SJSU-CMPE-195/group-project-group-22/hardware/schematics/Circuit Images/NeuronSynapseVersion1.jpg

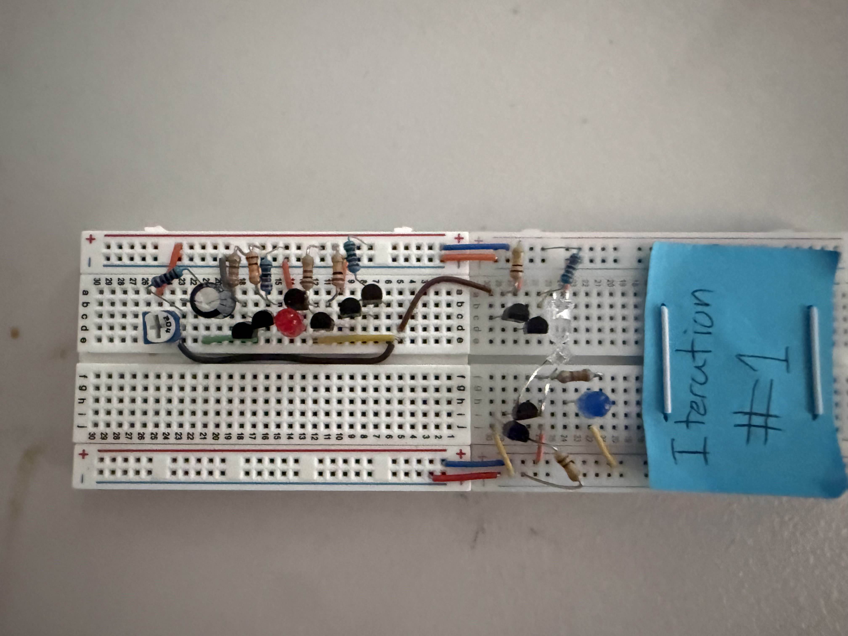
hardware/schematics/Circuit Images/NeuronSynapseVersion1.jpg
