SJSU-CMPE-195/group-project-group-22/hardware/schematics/Circuit Images/NeuronSynapseVersion2.jpg

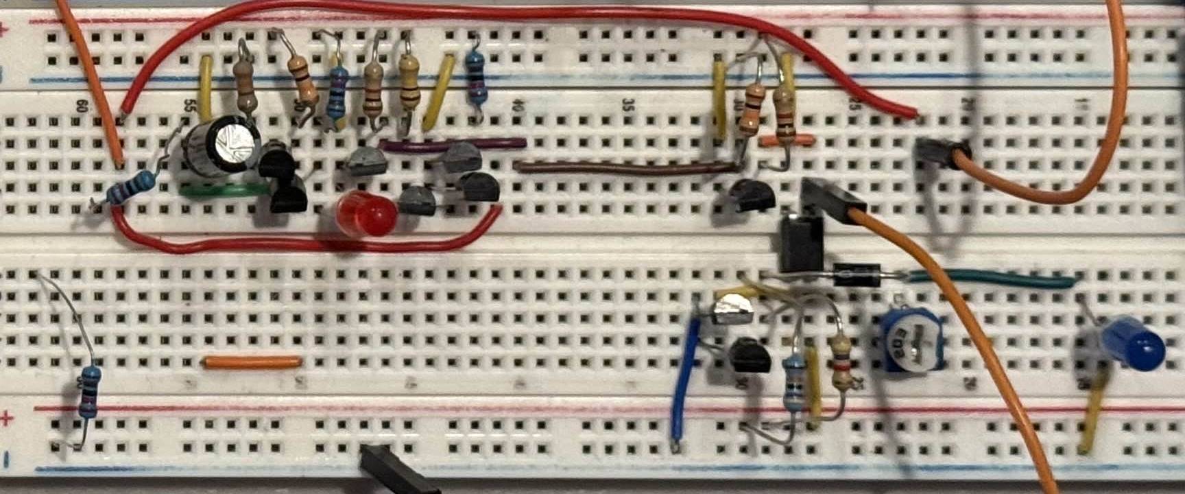
hardware/schematics/Circuit Images/NeuronSynapseVersion2.jpg
