SJSU-CMPE-195/group-project-group-22/hardware/pcb/PCB Soldering Images/PCB2.jpg

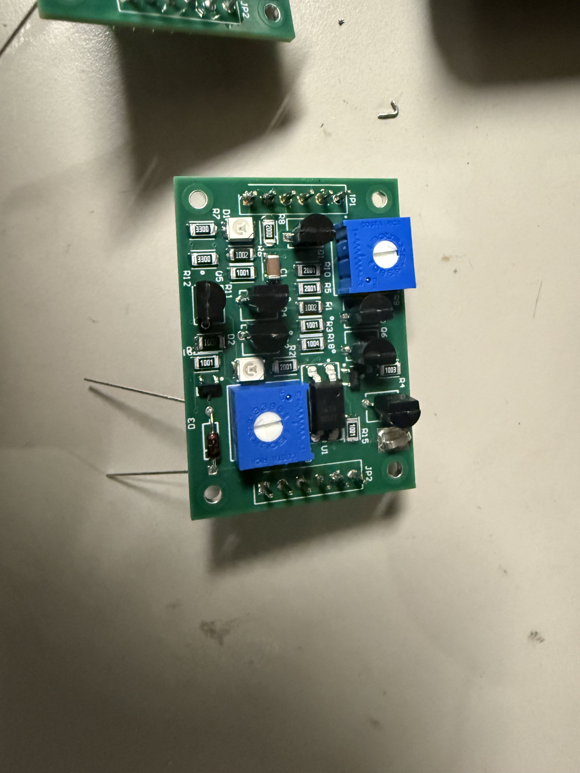
hardware/pcb/PCB Soldering Images/PCB2.jpg
