SJSU-CMPE-195/group-project-group-22/hardware/schematics/Neuron-Synapse-Version7-Schematic.asc

C1: cap; 47µF
C2: cap; 47µF
C3: cap; 47µF
D1: LED
D2: diode
D3: zener
D4: LED
D5: diode
D6: zener
D7: LED
D8: diode
D9: LED
M1: nmos; 2N7002
M2: nmos; 2N7002
M3: nmos; 2N7002
M4: nmos; 2N7002
M5: nmos; 2N7002
M6: nmos; 2N7002
Q1: npn; 2N2222
Q2: npn; 2N2222
Q3: npn; 2N2222
Q4: npn; 2N2222
Q5: npn; 2N2222
Q6: npn; 2N2222
Q7: npn; 2N2222
Q8: npn; 2N2222
Q9: npn; 2N2222
Q10: npn; 2N2222
Q11: npn; 2N2222
Q12: npn; 2N2222
Q13: npn; 2N2222
Q14: npn; 2N2222
Q15: npn; 2N2222
Q16: npn; 2N2222
Q17: npn; 2N2222
Q18: npn; 2N2222
Q19: npn; 2N2222
R1: res; 50k
R2: res; 2k
R3: res; 330
R4: res; 10k
R5: res; 2k
R6: res; 1k
R7: res; 100k
R8: res; 2k
R9: res; 1K
R10: res; 1000k
R11: res; 10k
R12: res; 1k
R13: res; 2K
R14: res; 150k
R15: res; 2k
R16: res; 330
R17: res; 2k
R18: res; 10k
R19: res; 1k
R20: res; 100k
R21: res; 2k
R22: res; 1k
R23: res; 1000k
R24: res; 10k
R25: res; 1k
R26: res; 10K
R28: res; 2k
R29: res; 330
R30: res; 2k
R31: res; 10k
R32: res; 1k
R33: res; 100k
R34: res; 2k
R35: res; 1k
R36: res; 1000k
R37: res; 10k
R38: res; 1k
R39: res; 2k
R40: res; 3k
R41: res; 220
U1: PC817C
U2: PC817C
U3: PC817C
V1: voltage; 5V
Named nets: 0, Vfb, Vfb2, Vfb3
.tran 10
.ic V(n014)=0 V(n015)=0
