SJSU-CMPE-195/group-project-group-22/hardware/schematics/Single-Neuron-V1-Schematic.asc

B1: bi; I=I(D2)*0.001
C1: cap; 47ľF
D1: LED
D2: LED
D3: LED
D4: diode
Q1: npn; 2N2222
Q2: npn; 2N2222
Q3: npn; 2N2222
Q4: npn; 2N2222
Q5: npn; 2N2222
Q6: npn; 2N2222
Q7: npn; 2N2222
Q8: npn; 2N2222
Q9: npn; 2N2222
Q10: npn; 2N2222
R1: res; 100k
R2: res; 2k
R3: res; 330
R4: res; 10k
R5: res; 2k
R6: res; 1k
R7: res; 100k
R8: res; 2k
R9: res; 100k
R10: res; 2k
R11: res; 100k
R12: res; 220
V1: voltage; 5V
Named nets: 0, SynOut, Nout
.tran 10
